BobGlicksman/WaterLeakSensor/WLD Read Me First.pdf

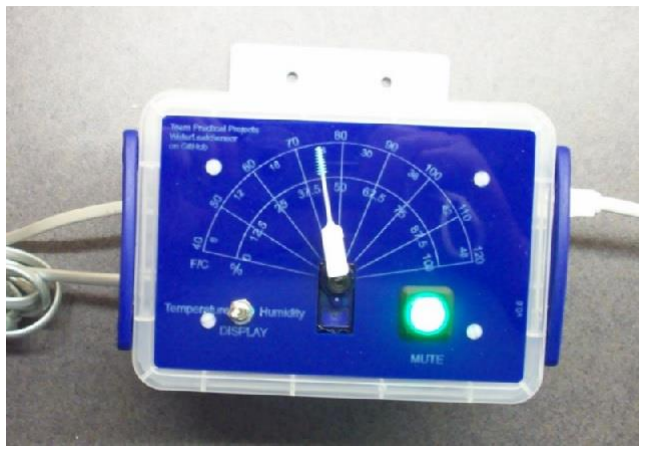
[picture p3: figure]

© 2022, 2017 Jim Schrempp and Bob Glicksman. All Rights Reserved

# Water Leak Detector - Read Me First

By: Jim Schrempp and Bob Glicksman; updated 12/25/2022

This document is © Copyright 2022, 2017 Team Practical Projects, Bob Glicksman and Jim Schrempp. All rights reserved.

NOTICE: Use of this document is subject to the terms of use described in the

document “Terms_of_Use_License_and_Disclaimer” that is included in this release package. This document can also be found at: https://github.com/TeamPracticalProjects/WaterLeakSensor/blob/master/Documentation/Terms_of_Use_License_and_Disclaimer.pdf

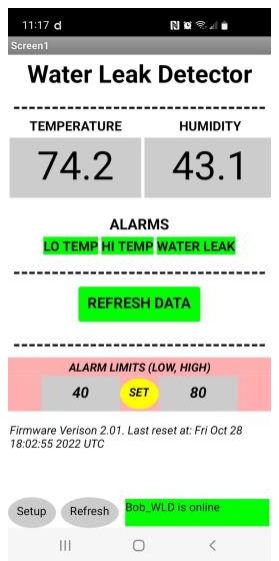
[picture p4: figure]

© 2022, 2017 Jim Schrempp and Bob Glicksman. All Rights Reserved

Table of Contents.

Table of Contents. | 2
1. Welcome. | 3
2. Review This Material Before Proceeding! | 4
3. Order of Assembly. | 6
4. Choosing The Best Enclosure For You | 8
5. Overview of the WLD Project Documentation. | 10
5.1. CASE Folder. | 10
5.2. DOCUMENTATION Folder. | 11
5.3. APP Folder. | 11
5.4. FIRMWARE Folder. | 11
5.5. SCRIPTS Folder. | 11
5.6. HARDWARE Folder. | 12
5.7. GRAPHICS Folder. | 12

© 2022, 2017 Jim Schrempp and Bob Glicksman. All Rights Reserved

1. Welcome.

Welcome to the Water Leak Detector project! The Water Leak Detector (WLD) is an IoT device that can monitor two specific locations for the presence of water. When water is detected an alarm will sound and an SMS text alert will be sent to a mobile phone. The WLD also includes a temperature and humidity sensor. These values are displayed on a dial and also on a smartphone app. The smartphone app allows the user to set low and high temperature alarm limits and out-of-bounds temperature readings result in SMS text alerts to the user’s mobile phone.

This document will help you to decide whether you should proceed to purchase parts and materials and proceed to build a WLD for yourself or for others. If you decide to proceed and build one or more WLDs, this document will serve as a top level guide through our extensive documentation. All of the documentation for this project is sourced and maintained at:

https://github.com/TeamPracticalProjects/WaterLeakSensor/tree/master

Please carefully review this entire document before deciding to proceed with this project:

Section 2 of this document contains a list of materials that you should review before you decide to order parts, materials and/or begin construction of a WLD. We strongly recommend that you review this material in order to ensure that you have the skills, tools and facilities to undertake a project of this complexity.

Section 3 of this document provides you with an overview of the complete contents of the GitHub repository where we maintain the project documentation. You will need to refer to this section in order to locate the documents, firmware files, CAD files, and other material that you will need in order to build, install and test a WLD.

Section 4 of this document provides you with a selection guide for the three enclosures that we have designed and documented. You only need one enclosure for this project. Owing to the cost and complexity of the enclosure, we have provided three different designs for you to choose from. Choose only one of these designs for your project enclosure. It is important for you to make your decision up front, so that you order only the parts and materials that you will be needing to build your WLD.

Section 5 of this document contains an overview of the folders and files in this repository.

© 2022, 2017 Jim Schrempp and Bob Glicksman. All Rights Reserved

# 2. Review This Material Before Proceeding!

We strongly recommend that you review all of the following documents before proceeding further with this project. We are not responsible if you purchase parts and materials for this project and later discover that you do not have the necessary skills, tools, facilities or time to complete it!

- You MUST agree to our terms of use, license and disclaimer requirements and limitations before proceeding further. The following document contains these details:

“Terms_of_Use_License_and_Disclaimer.pdf”, which is located in the Documentation folder in this repository.

By proceeding past this point, you implicitly agree with everything in this document!

- We recommend that you review the WLD concept document:

“Water_Leak_Detector_Concept_V2.pdf”, which is located in the Documentation folder in this repository.

This Concept document will help you understand what the WLD is and whether or not a WLD will meet your needs and expectations.

- We strongly recommend that you review the WLD Installation and User Manual:

“WLD_Installation_and_Userr_Manual_V2.pdf”, which is located in the Documentation folder in this repository.

This document will provide you with insight about what this project consists of and what infrastructure is required to install and operate the WLD.

- We also strongly recommend that you review the WLD Frequently Asked Questions document, at:

“WLD_FAQ.pdf”, which is located in the Documentation folder in this repository.

Please pay particular attention to the Building/Installing questions in order to ensure that you have the proper tools, materials, and infrastructure to build and install a WLD.

- You will also need accounts with particle.io, Google, and a mobile phone carrier (for your smartphone). These accounts are free or included with your purchase, but you do need

© 2022, 2017 Jim Schrempp and Bob Glicksman. All Rights Reserved to register with these sites. You do not need to know how to write software, but you do need to carefully follow the instructions that we provide in order to install our software on your Photon device, your smartphone, and in the cloud.

© 2022, 2017 Jim Schrempp and Bob Glicksman. All Rights Reserved

3. Order of Assembly.

The WLD build process consists of a number of steps. Each step completes a module in the overall process. While you can do steps in a different order, we have provided you what we think is the most straightforward path to success:

1. Choose the enclosure you want to use. You have 3 choices:
a. Plastic box
b. 3D printed chassis
c. Laser cut wooden box

Read below (section 4) in this document for help in choosing the best enclosure for you.

### 2. Obtain all the parts from the parts list. The parts list can be found at:

“WaterLeakAlarmPartsList.pdf”, which is located in the Documentation folder in this repository.

Note that the Parts List has a required section and then sections for each of the enclosure options. You will need to obtain all required parts and also those parts listed for the enclosure option that you chose in the step above.

3. Assemble the printed circuit board and RJ11 breakout boards. Once you have obtained the necessary parts, proceed to assemble the printed circuit boards following the instructions at:

“PCB Assembly Instructions.pdf”, which is located in the Documentation folder in this repository.

4. Assemble the enclosure that you selected. Use the set of instructions that pertain to your selected enclosure option:
- Cut plastic box:

“Enclosure Build Instructions Plastic Case.pdf”, which is located in the Documentation folder in this repository.

- 3D printed enclosure:

“Enclosure Build Instructions 3D Printed.pdf”, which is located in the Documentation folder in this repository.

© 2022, 2017 Jim Schrempp and Bob Glicksman. All Rights Reserved

- 2D cut enclosure:

“Enclosure Build Instructions 2D Box.pdf”, which is located in the Documentation folder in this repository.

5. Install the Water Leak Detector firmware. Instructions can be found at:

“WLD_Installation_and_User_Manual_V2.pdf”, section 6.1, which is located in the Documentation folder in this repository.

Note that you will need to first install the servo calibration firmware and calibrate the servo meter on the front face of the WLD. You will then have to install the operating firmware and test it out, per section 7 of this document.

6. Install the Google Apps Script and Particle Webhook. Instructions can be found at:

“WLD_Installation_and_User_Manual_V2.pdf”, section 6.3, which is located in the Documentation folder in this repository.

7. Install the Smartphone App on your mobile phone (optional). Instructions can be found at:

“WLD_Installation_and_User_Manual_V2.pdf”, section 6.2, which is located in the Documentation folder in this repository.

8. Install the WLD and test it. Instructions can be found at:

“WLD_Installation_and_User_Manual_V2.pdf”, sections 3 and 7, which is located in the Documentation folder in this repository.

© 2022, 2017 Jim Schrempp and Bob Glicksman. All Rights Reserved

# 4. Choosing The Best Enclosure For You

The WLD provides instructions for three different enclosures: plastic box, 2D box, 3D printed chassis. Which one you use depends on you. Choose only one of these options before proceeding to order parts and materials.

1. If you are price sensitive, the plastic box is the least expensive option. This uses a $3 plastic box available from your local office supply store or over the Internet.
2. If you have access to a laser cutter, then the laser cut box is a nice upgrade from the plastic box. The laser cut box can have a beautiful etched dial and be either enclosed or open in design. You could also carefully cut and drill these parts by hand.
3. If you want the most professional looking device, the 3D printed chassis is for you. You can order the chassis and bezel from Shapeways for about $40. Or if you have your own 3D printer, then you can print the chassis and bezel for a few dollars in material, using the CAD files that we provide..
| Plastic Box | 2D Cut Box | 3D Printed Box
Pro | ● Cheap ● Sturdy | ● Looks very good ● Simple to make ● Offers a few choices of style | ● Looks professional ● Really, it looks great ● Print it on your own 3D printer at low cost
Con | ● Looks DIY ● Cut it yourself ● Dial is cardboard Or laser etched | ● Need a laser cutter Or a coping saw. | ● Need a 3D printer
Buy | | | Buy from Shapeways for $40

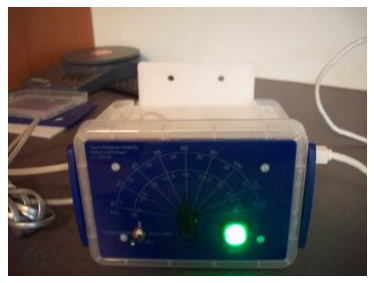
[picture p5: figure]
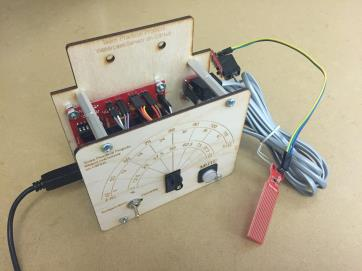
[picture p6: figure]

© 2022, 2017 Jim Schrempp and Bob Glicksman. All Rights Reserved

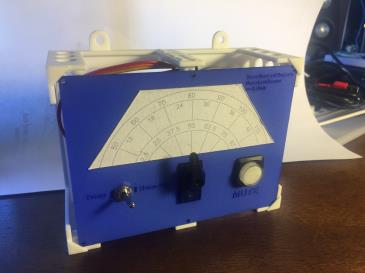
[picture p7: figure]

Photos of: (left) Plastic Box (with laser cut faceplate), (center) Laser Cut Box, (right) 3D Printed Box.

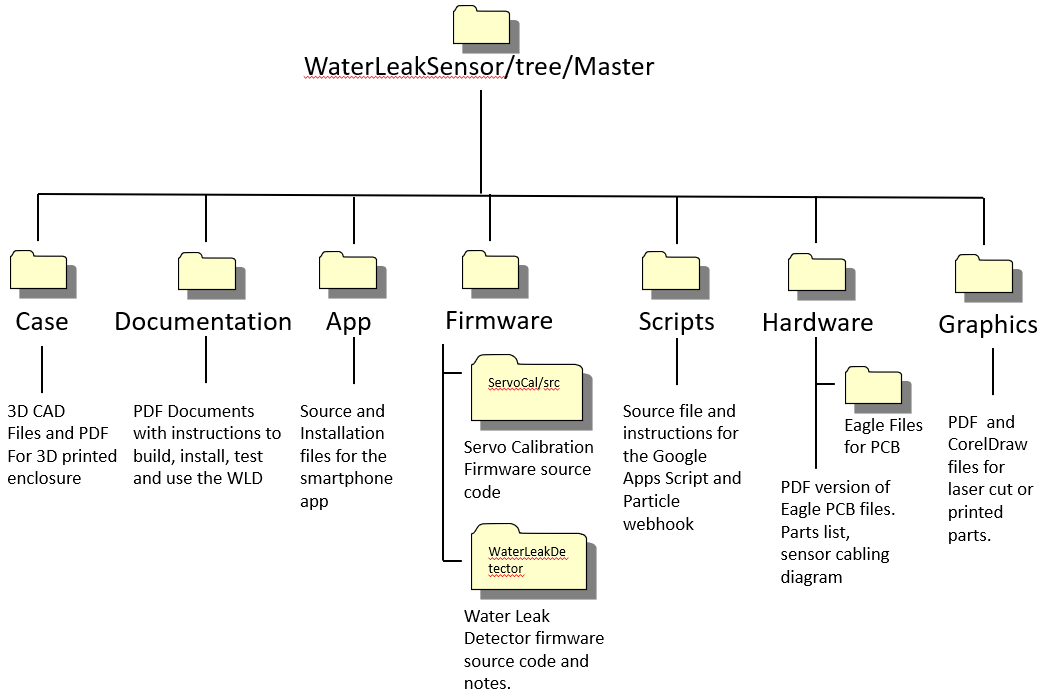
[picture p8: figure]

© 2022, 2017 Jim Schrempp and Bob Glicksman. All Rights Reserved

5. Overview of the WLD Project Documentation.

The figure below depicts the documentation tree for the WLD project. The WLD project files are posted and maintained in the GitHub repository: https://github.com/TeamPracticalProjects/WaterLeakSensor

5.1. CASE Folder.

The CASE folder contains 3D CAD files for manufacturing the enclosure skeleton and the bezel. Free CAD source files are provided under the open source license for this project. Use these files if you want to modify our case design:
- casebottomskel.FCStd (enclosure chassis)
- casebezel.FCStd (bezel)

If you want to use our case and bezel designs as is, you can buy them off of the Parts List from Shapeways, or you can use the following files with a 3D printer of your choice:
- casebottomskel.stl
- casebezel.stl

© 2022, 2017 Jim Schrempp and Bob Glicksman. All Rights Reserved

We have also provided a PDF version of the bezel design: casebezel.pdf

5.2. DOCUMENTATION Folder.

This folder contains the Parts List and all of the human readable documentation for the WLD project. This documentation contains the Concept Document, Terms of Use License and Disclosure Document, the installation and user manual, assembly instruction documents for each of the assembly steps described in section 3, above, a Troubleshooting document and some handy Frequently Asked Questions (FAQ) and answers.

5.3. APP Folder.

The APP folder contains source code and the installation file for the smartphone App that is part of this project. The installation file: “WaterLeakDetectorApp.apk” can be loaded on any Android smartphone and then tapped on to install the App. The source code file: “WaterLeakDetectorApp.aia” is provided for those users who wish to understand and perhaps modify the App. The source code is for MIT App Inventor 2 (http://ai2.appinventor.mit.edu/) . The App is only available for Android smartphone at this time (iOS support is in process but not yet released by MIT). The document: “WLD_Installation_and_User_Manual_V2.pdf”, section 6.2, in the Documentation folder of this repository, contains installation instructions for the App.

5.4. FIRMWARE Folder.

The FIRMWARE folder contains two subfolders:
- ServoCal/src: contains the source code (.ino file) for the servo calibration software.
- WaterLeakDetector: contains an src subfolder that has the source code for the Photon in the WLD (.ino file).

The document: “WLD_Installation_and_User_Manual_V2.pdf”, section 6.1, in the Documentation folder of this repository, contains installation and servo calibration instructions for the WLD firmware.

5.5. SCRIPTS Folder.

The Scripts folder contains the source code for the Google Apps Script that is needed to send SMS text alarms to a mobile phone. This folder also contains the webhook configuration information for the Particle webhook that fires off the Script whenever the WLD firmware publishes an alarm event to the Particle cloud. The document: “WLD_Installation_and_User_Manual_V2.pdf”, section 6.3, in the Documentation folder of this repository, contains installation instructions for Script and the webhook.

© 2022, 2017 Jim Schrempp and Bob Glicksman. All Rights Reserved

5.6. HARDWARE Folder.

The HARDWARE folder contains .pdf files for the PCB schematic and board layout. It also contains a .pdf file describing the sensor wiring to the main PCB. The subfolder Eagle files contain the Eagle .sch and .brd files that can be used if you wish to modify our PCB design.

If you want to use our PCB as-is, then you can order one from the link to DirtyPCB.com in the parts list document.

5.7. GRAPHICS Folder.

The GRAPHICS folder contains the CorelDraw source file for all of the laser cut parts (CaseDial.cdr). Use this file if you wish to modify any of our 2D laser cut part designs. This folder also contains a .pdf version of this file (CaseDial.pdf). This latter file can be used to view the 2D drawings without needing the CorelDraw software. You can also use this file to print out full size renderings of the bezel scales for the 3D and cut plastic box enclosures. You can use these renderings as templates for cutting 2D parts and/or in lieu of laser engraving the servo meter face scale.
