BobGlicksman/WaterLeakSensor/Case/casebezel.pdf

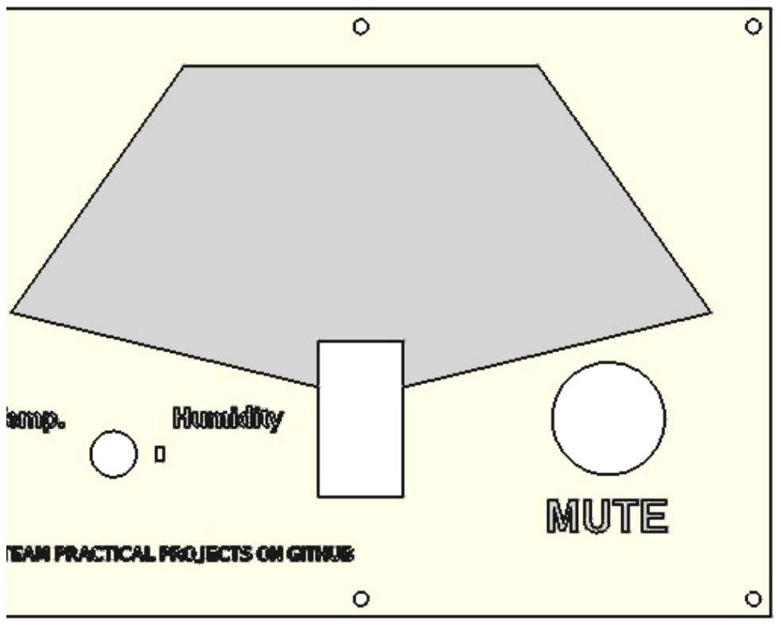
[picture p9: page 1]
