BobGlicksman/WaterLeakSensor/Graphics/CaseDial.pdf

F/C
%

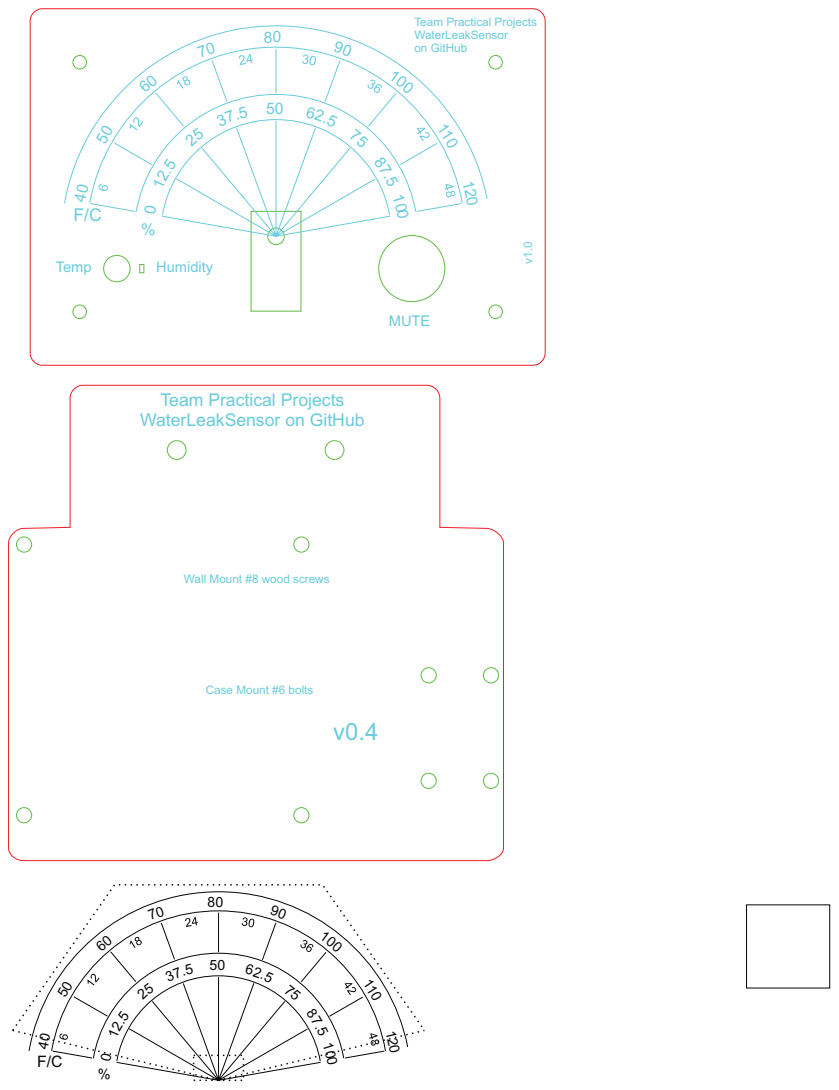
[picture p70: page 1]
MUTE; Temp; Humidity

Team Practical Projects
WaterLeakSensor
on GitHub

WaterLeakSensor on GitHub

Wall Mount #8 wood screws

Case Mount #6 bolts

## WaterLeakSensor on GitHub

# test

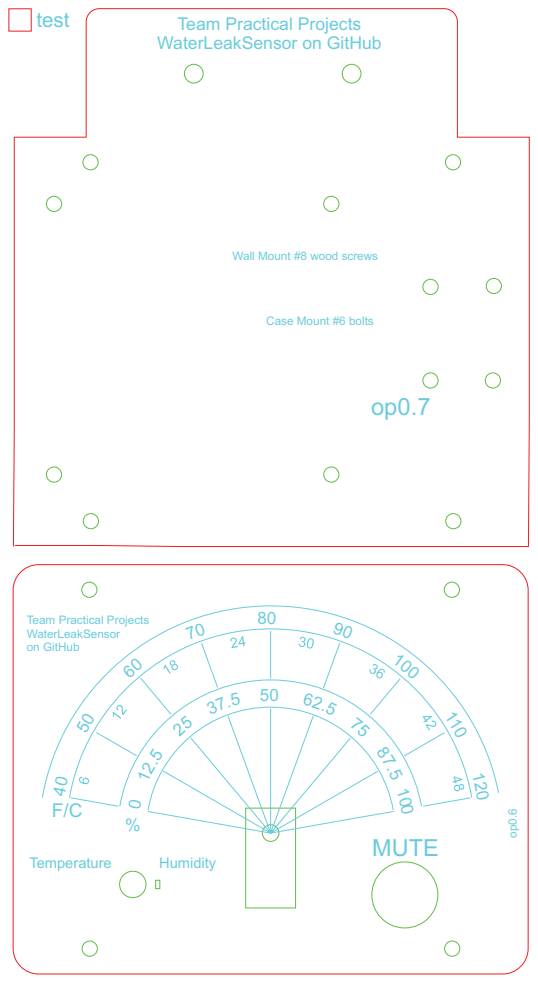
[picture p71: page 2]
MUTE; Temperature; Humidity

Wall Mount #8 wood screws

Case Mount #6 bolts

Team Practical Projects
WaterLeakSensor
on GitHub

## WaterLeakSensor on GitHub

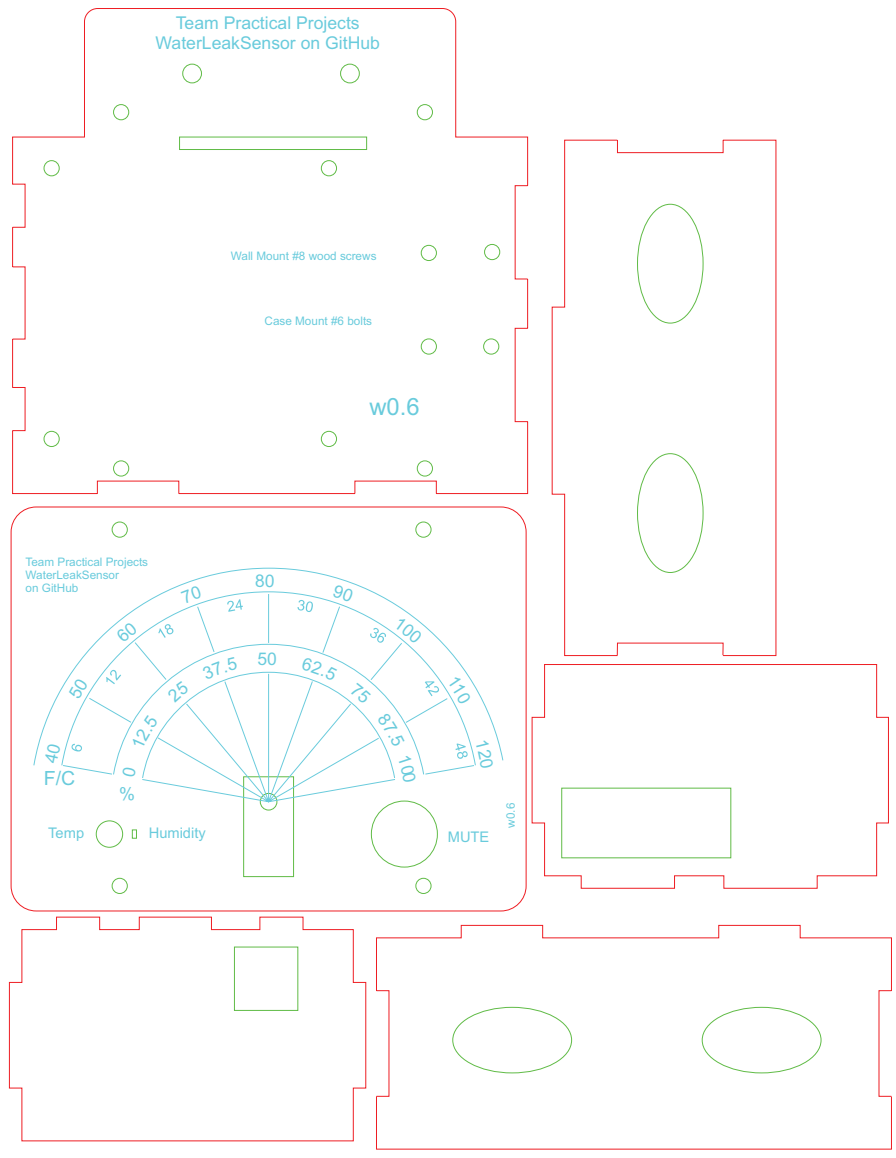
[picture p72: page 3]
MUTE; Temp; Humidity

Wall Mount #8 wood screws

Case Mount #6 bolts

Team Practical Projects
WaterLeakSensor
on GitHub
